rorosaurus/3ds-xl-usb-c/images/before-charge-port.jpg

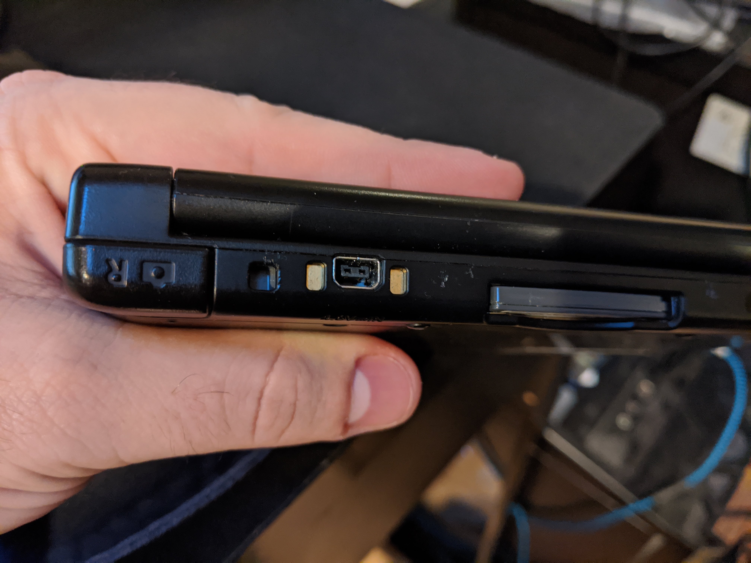
images/before-charge-port.jpg
