rorosaurus/3ds-xl-usb-c/images/before-port-top.jpg

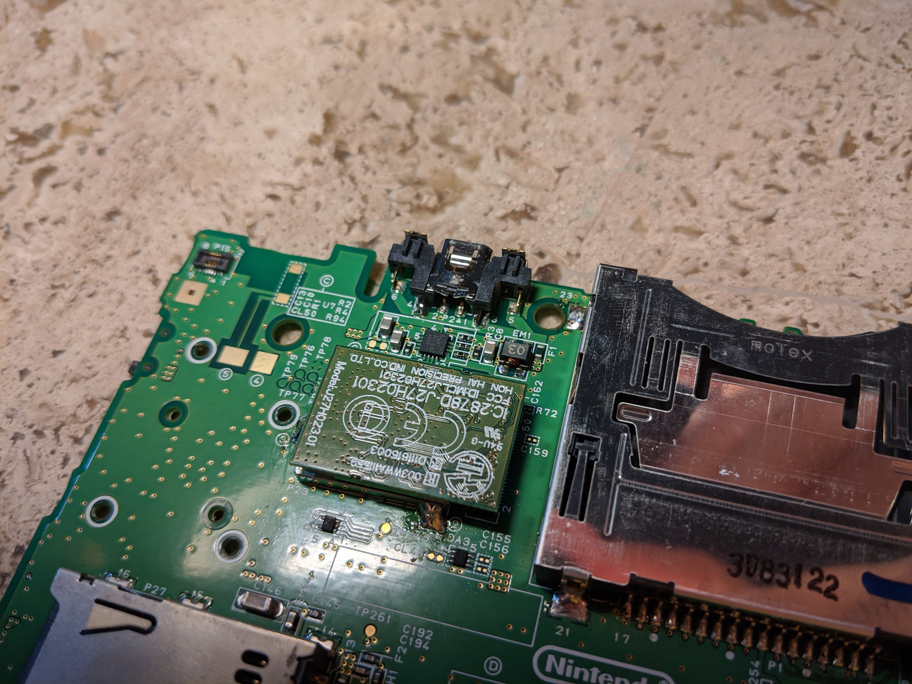
images/before-port-top.jpg
